dries007/Project2/Site/foto's/display_whole.jpg

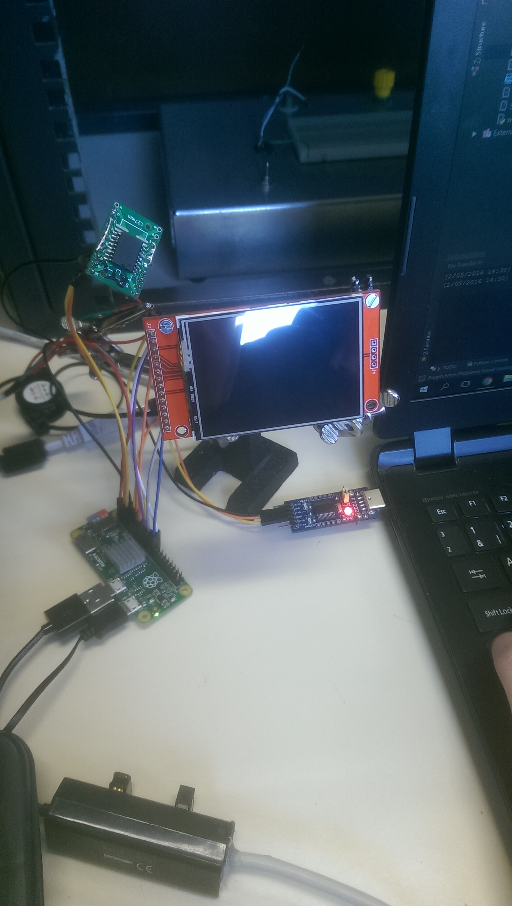
Site/foto's/display_whole.jpg
