dries007/Project2/Site/foto's/Pi zero.jpg

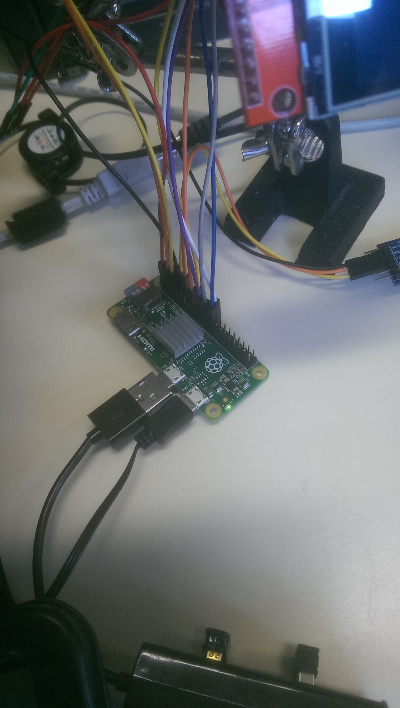
Site/foto's/Pi zero.jpg
