dries007/Project2/Site/foto's/RTC.jpg

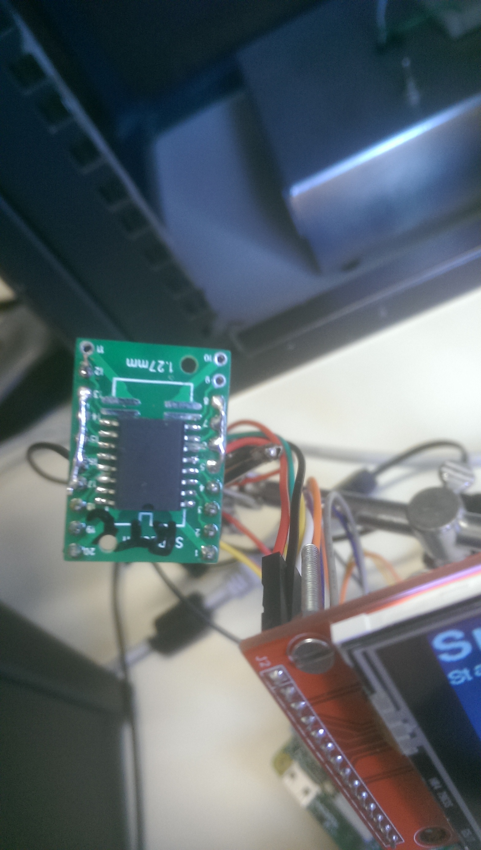
Site/foto's/RTC.jpg
