dries007/Project2/Site/foto's/screen.jpg

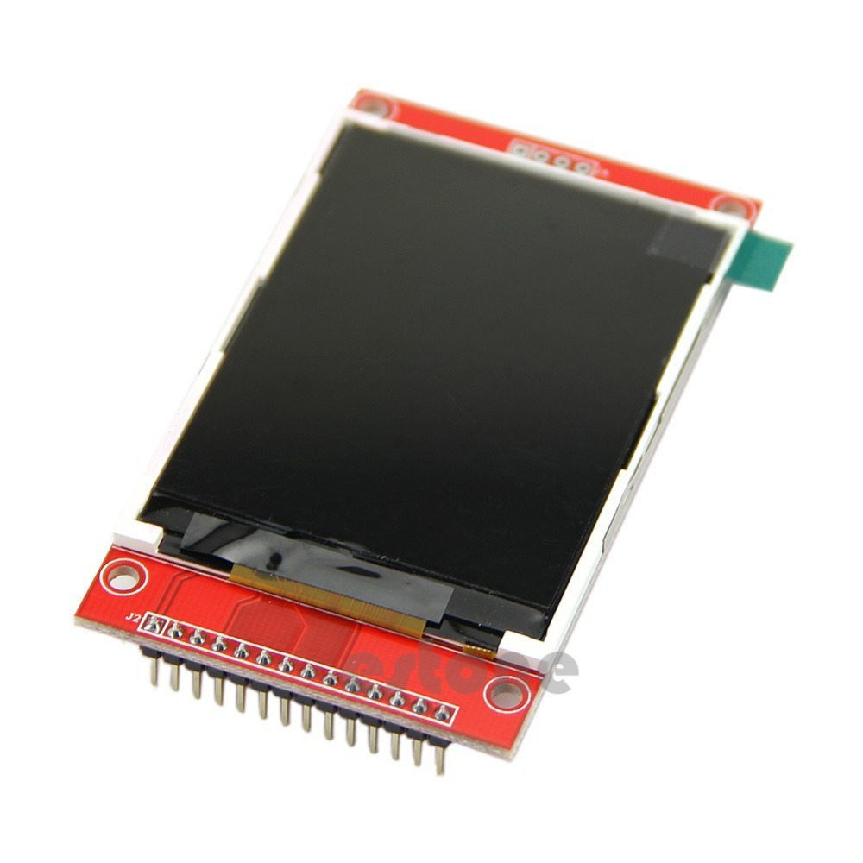
Site/foto's/screen.jpg
