dries007/Project2/Site/foto's/WiFidongle.jpg

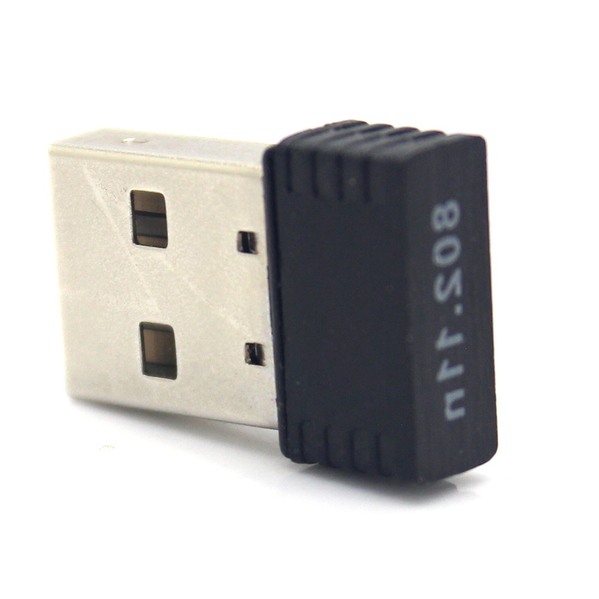
Site/foto's/WiFidongle.jpg
