dries007/Project2/Site/fotos/IMG_20160522_124822.jpg

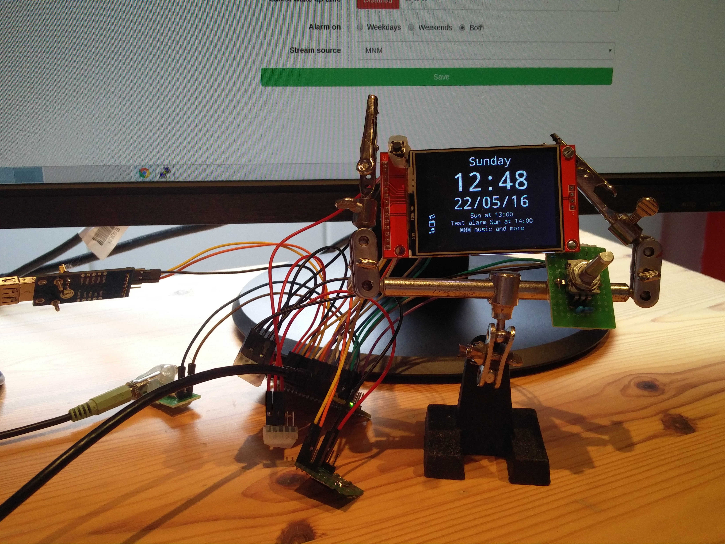
Site/fotos/IMG_20160522_124822.jpg
