dries007/Project2/Site/fotos/IMG_20160522_124845.jpg

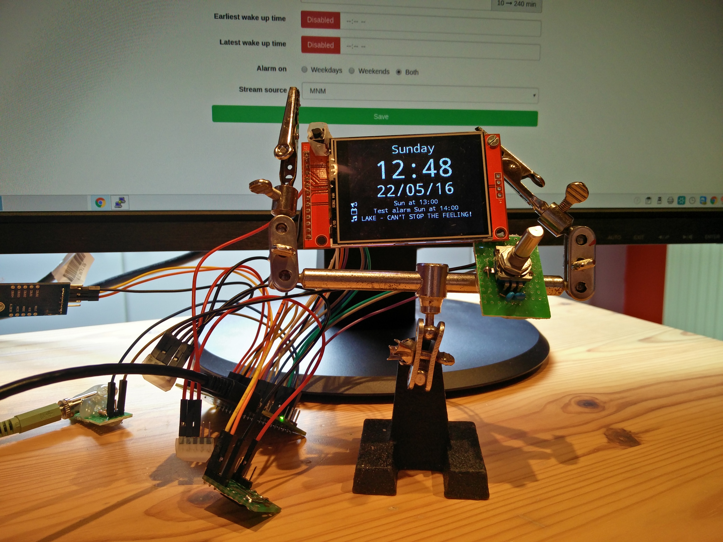
Site/fotos/IMG_20160522_124845.jpg
