dries007/Project2/Site/fotos/IMG_20160522_124852.jpg

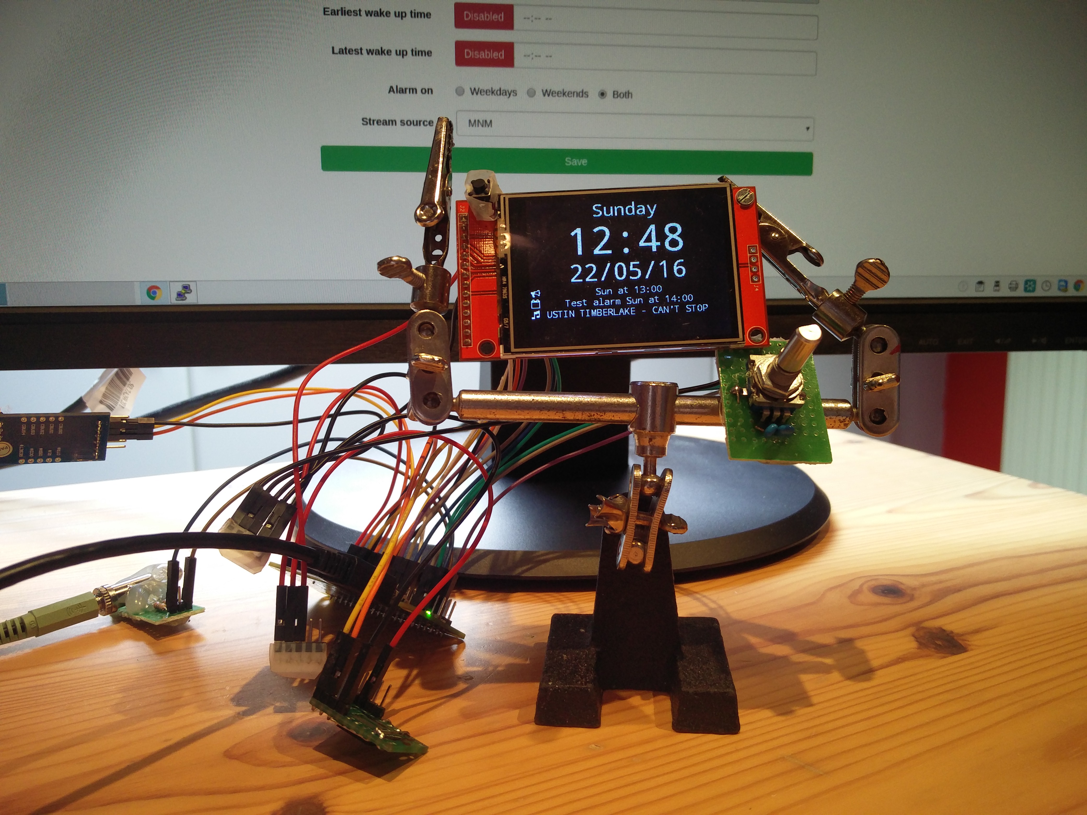
Site/fotos/IMG_20160522_124852.jpg
