dries007/Project2/Site/fotos/IMG_20160522_125030.jpg

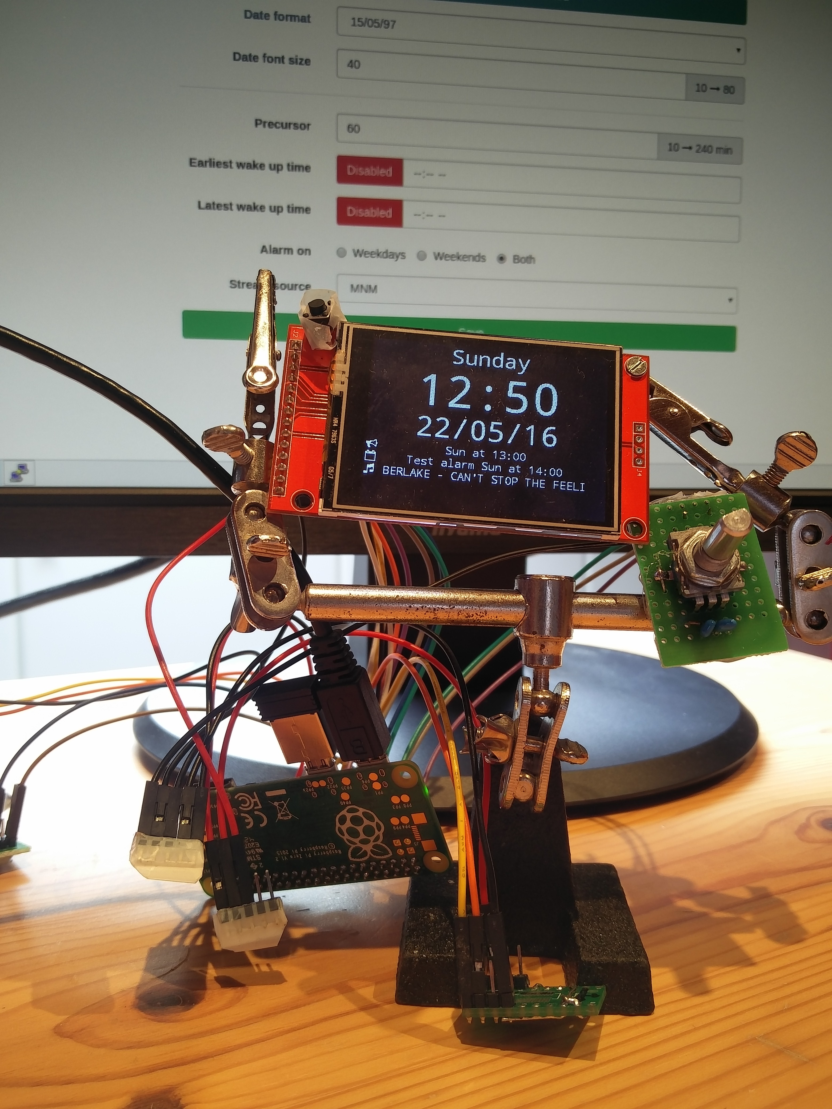
Site/fotos/IMG_20160522_125030.jpg
