dries007/Project2/Site/fotos/IMG_20160522_125043.jpg

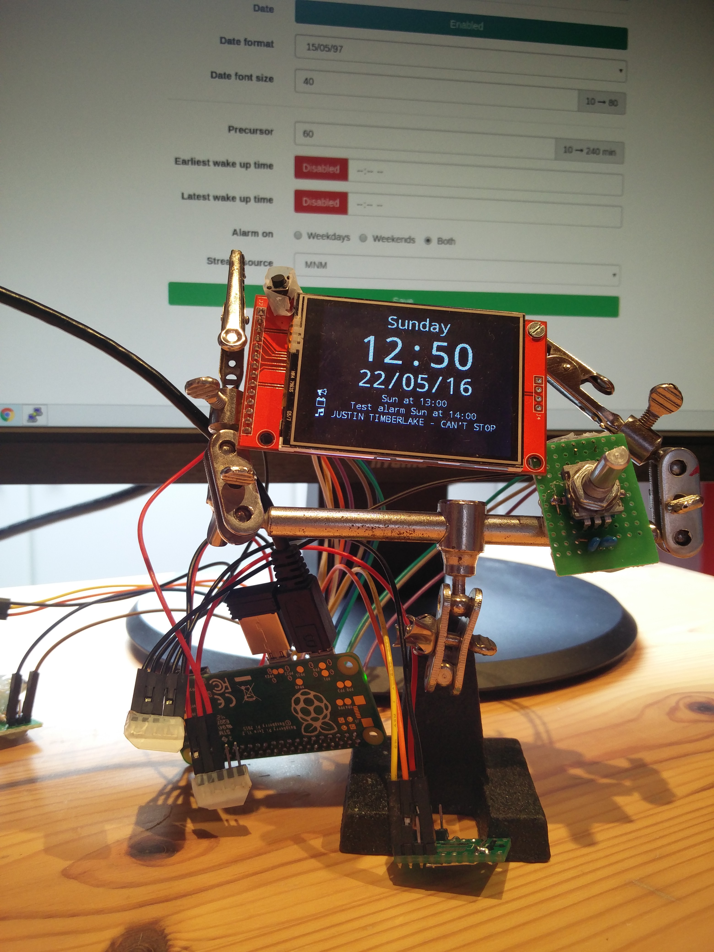
Site/fotos/IMG_20160522_125043.jpg
