dries007/Project2/Site/fotos/IMG_20160522_125055.jpg

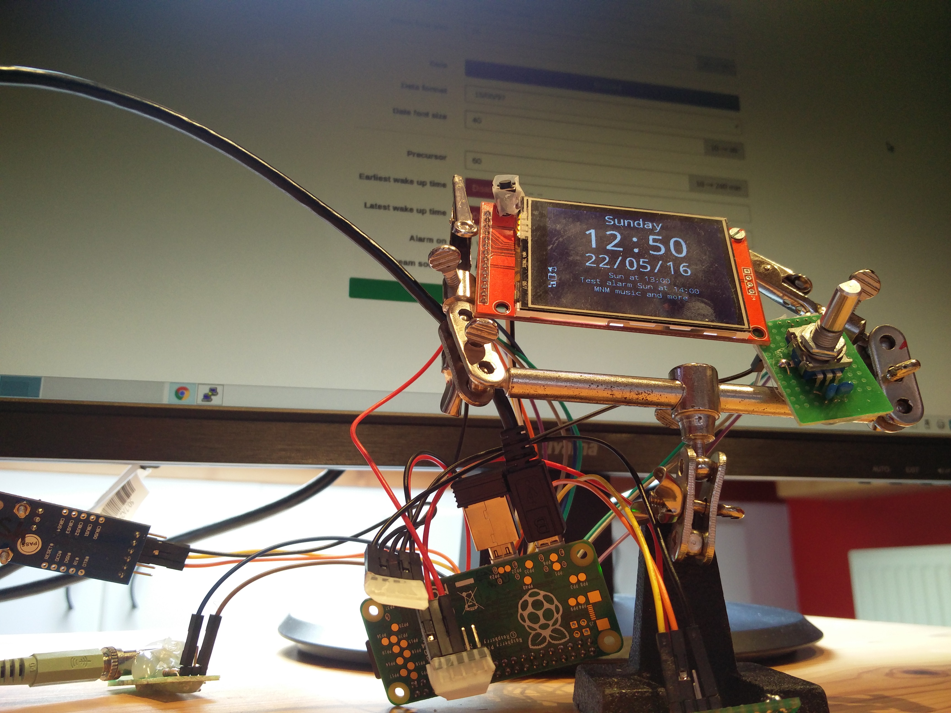
Site/fotos/IMG_20160522_125055.jpg
