dries007/Project2/Documents/Projectvoorstel.1.pdf

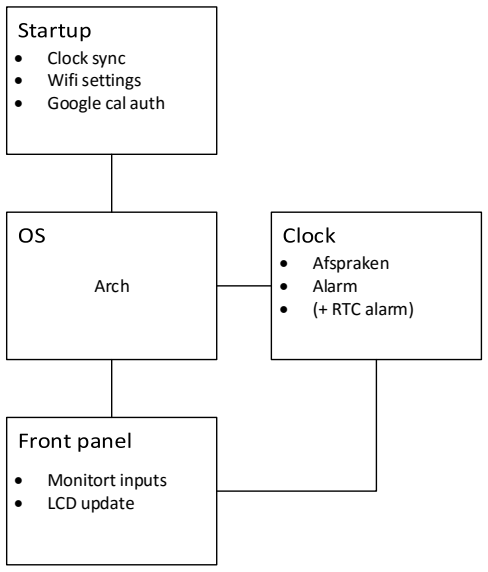
[picture p42: figure]
Arch; • Clock sync • Wifi settings • Google cal auth; • Afspraken • Alarm • (+ RTC alarm); • Monitort inputs • LCD update

Document Projectvoorstel Projecten1 | Pagina 1 van 2

## Projectvoorstel

### 1 Teamleden : Dries Kennes & Michiel Bellekens

### 2 Titel project: The smart clock

3 Korte omschrijving van het project.

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

4 Blokschema.

### 4.1 Software

Datum
goedkeuring

Versie Datum herziening

Redacteur(s)

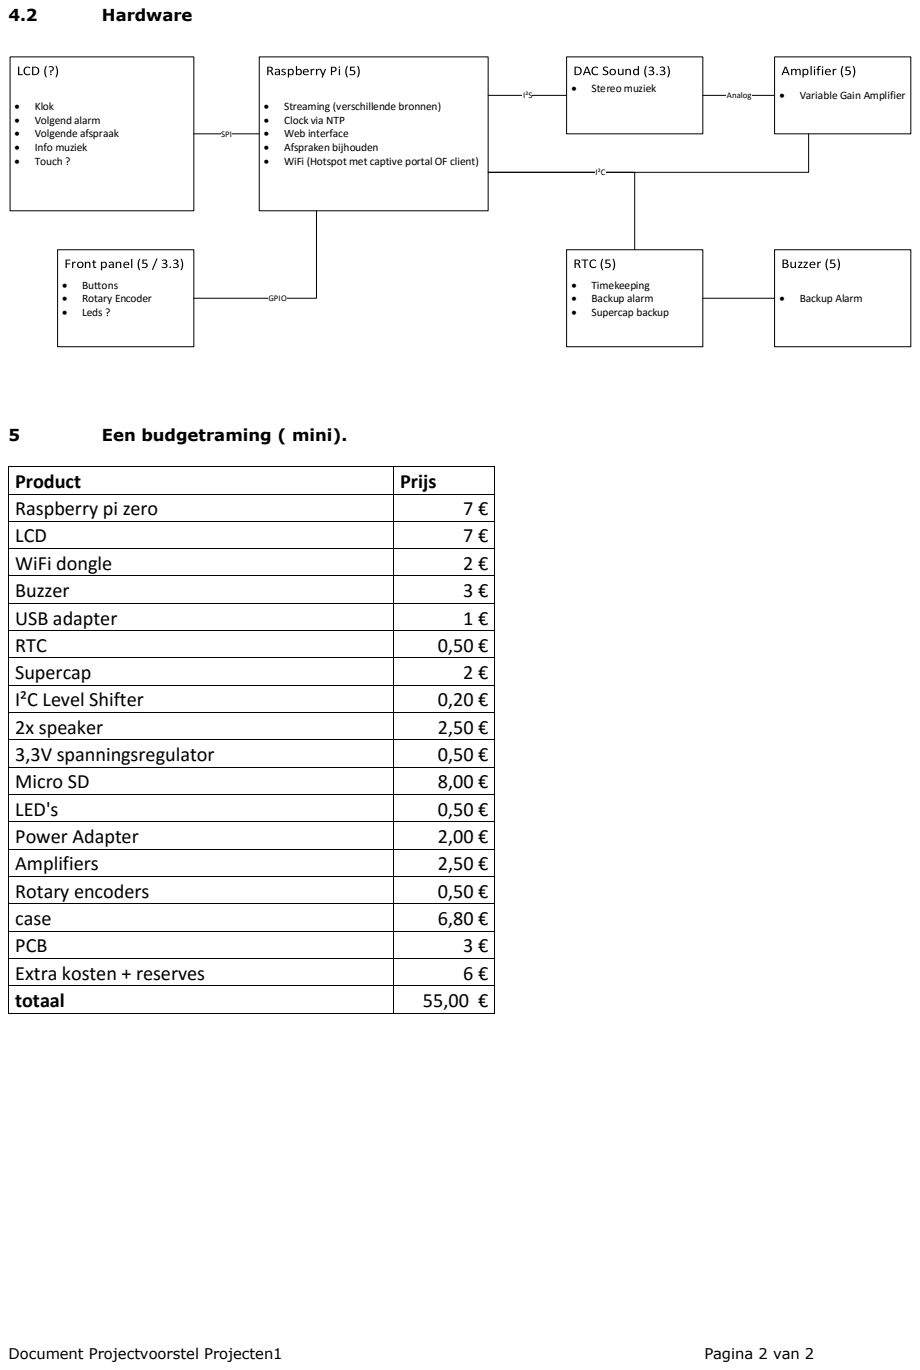
[picture p43: page 2]
Document Projectvoorstel Projecten1; Pagina 2 van 2; 4.2 Hardware; • Klok • Volgend alarm • Volgende afspraak • Info muziek • Touch ?; • Timekeeping • Backup alarm • Supercap backup; • Stereo muziek; • Buttons • Rotary Encoder • Leds ?; • Backup Alarm; SPI; I²S; GPIO; Analog; I²C

• Variable Gain Amplifier

• Streaming (verschillende bronnen)
• Clock via NTP
• Web interface
• Afspraken bijhouden
• WiFi (Hotspot met captive portal OF client)

5 Een budgetraming ( mini).

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
